pinae/AeVOC/src/oledFunctions.cpp

#include <Arduino.h>
#include <Adafruit_GFX.h>
#include <Adafruit_SSD1306.h>
#include "configHelpers.h"

extern Adafruit_SSD1306 display;

void drawBarDiagram(int16_t y, float value, float minVal, float maxVal) {
  display.drawRect(73, y, 128-73, 7, WHITE);
  display.fillRect(73, y, 
    (int) round((value-minVal)/(maxVal-minVal)*(128-73)), 
    7, WHITE);
}

void displayMeasurements(float pm25, float pm10, 
        uint16_t co2, uint16_t voc, 
        float temperature, float humidity) {
  display.clearDisplay();
  display.setTextSize(1); 
  display.setTextColor(WHITE);
  display.setCursor(0, 16);
  display.cp437(true);
  display.printf("PM2,5: %2.2f\n", pm25);
  drawBarDiagram(16, pm25, PM25_MINIMUM, PM25_EXTREME);
  display.printf("PM10: %2.2f\n", pm10);
  drawBarDiagram(24, pm10, PM10_MINIMUM, PM10_EXTREME);
  display.printf("CO2: %u ppm\n", co2);
  drawBarDiagram(32, (float) co2, CO2_MINIMUM, CO2_EXTREME);
  display.printf("VOC: %u ppb\n", voc);
  drawBarDiagram(38, (float) voc, VOC_MINIMUM, VOC_EXTREME);
  display.printf("%2.1f\n", temperature);
  display.drawCircle(26, 49, 1, WHITE);
  display.drawChar(29, 48, 'C', WHITE, BLACK, 1);
  drawBarDiagram(46, temperature, TEMP_MINIMUM, TEMP_EXTREME);
  display.drawLine(3, 56, 0, 59, WHITE);
  display.drawLine(0, 59, 0, 61, WHITE);
  display.drawLine(0, 61, 2, 63, WHITE);
  display.drawLine(2, 63, 4, 63, WHITE);
  display.drawLine(4, 63, 6, 61, WHITE);
  display.drawLine(6, 61, 6, 59, WHITE);
  display.drawLine(6, 59, 3, 56, WHITE);
  display.printf("  %2.0f%%", humidity);
  drawBarDiagram(54, humidity, HUMIDITY_MINIMUM, HUMIDITY_EXTREME);
  display.setTextSize(2);
  display.setCursor(0, 0);
  char topText[12];
  sprintf(&topText[0], "Alles OK.");
  if (co2 > 1000) sprintf(&topText[0], "CO2: zzz..");
  if (co2 > 1500) sprintf(&topText[0], "Zuviel CO2");
  if (humidity > 67) sprintf(&topText[0], "Schimmel!");
  if (voc > 550) sprintf(&topText[0], "Gestank!");
  if (pm25 > 6.0f || pm10 > 15.0f) sprintf(&topText[0], "Aerosole!");
  display.println(topText);
  display.display();
}
