pinae/AeVOC/src/neopixelMatrix.h

float normValue(float val, float minVal, float maxVal);
bool sanityCheck(float val, float minVal, float maxVal);
bool sanityCheck(uint16_t val, uint16_t minVal, uint16_t maxVal);
float maxOf(float a, float b);
void shiftPmMeasurements(float pm);
void addPmMeasurement(float pm);
void shiftVocMeasurements(float voc);
void addVocMeasurement(float voc);
void displayMatrix();
